RBSC/YamahaVideoBoard/Pics/board.jpg

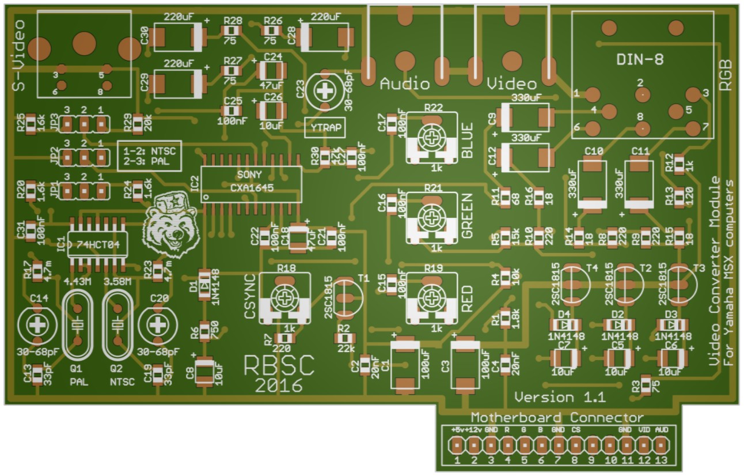
Pics/board.jpg
