RBSC/YamahaVideoBoard/Pics/board_top.png

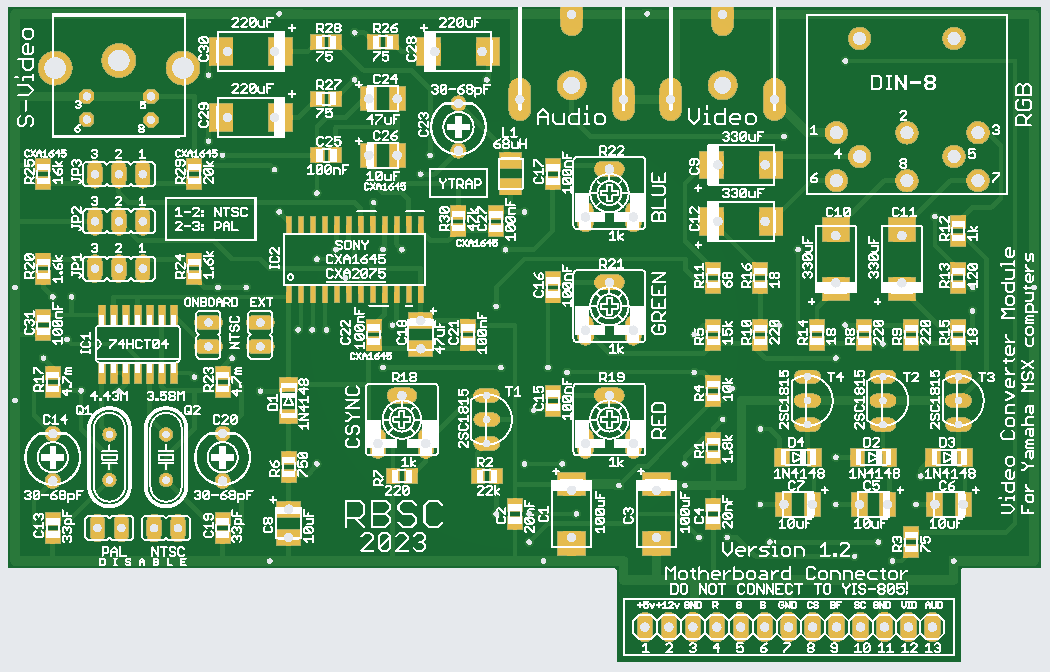
Pics/board_top.png
