RBSC/YamahaVideoBoard/Pics/elcaps_board.jpg

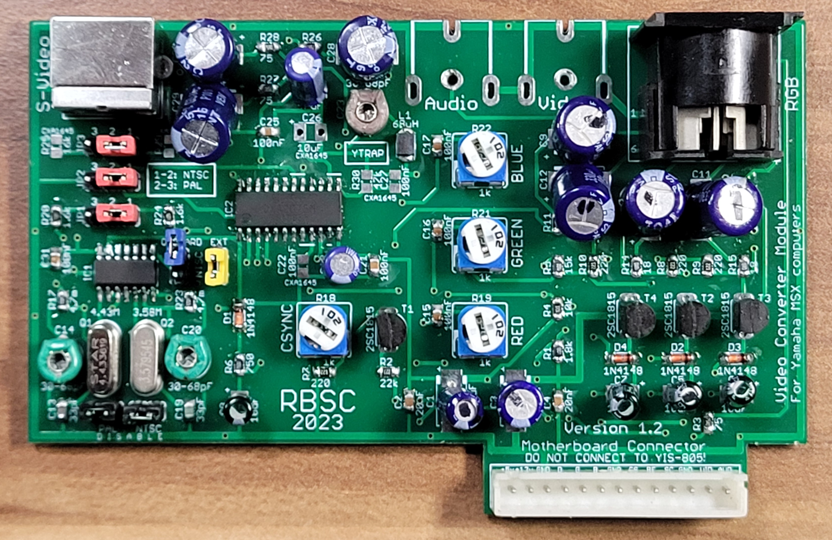
Pics/elcaps_board.jpg
