RBSC/YamahaVideoBoard/Pics/realboard.jpg

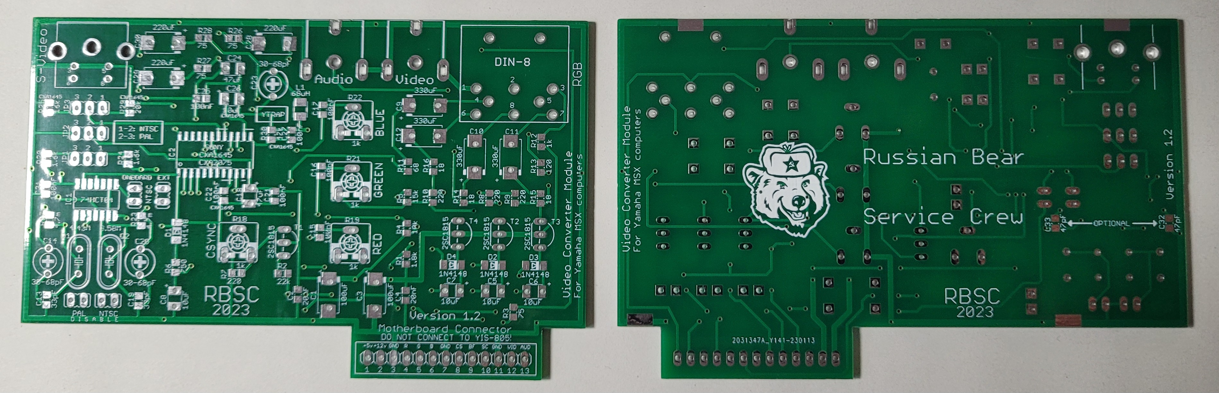
Pics/realboard.jpg
